Viproz/TNEV-Project/src/UltrasonicSensorCarriage.h

/* 
 * File:   UltrasonicSensorCarriage.h
 * Author: viproz
 *
 * Created on 17 mai 2015, 20:25
 */

#ifndef ULTRASONICSENSORCARRIAGE_H
#define	ULTRASONICSENSORCARRIAGE_H
#include "UltrasonicSensor.h"
#include "Servo.h"
#include <Arduino.h>

class UltrasonicSensorCarriage {
public:
    UltrasonicSensorCarriage();
    virtual ~UltrasonicSensorCarriage();
    void findNearest(int& angle, int& distance);
    int getDistance();
    void reset();
    void write(int angle) { servo->write(angle); }
private:
    Servo* servo;
    UltrasonicSensor* sensor;
    
};

#endif	/* ULTRASONICSENSORCARRIAGE_H */
