Viproz/TNEV-Project/src/Button.cpp

/* 
 * File:   Button.cpp
 * Author: viproz
 * 
 * Created on 31 mai 2015, 17:24
 */

#include "Button.h"

Button::Button(uint8_t pinButton) :
    pinButton(pinButton) {
    pinMode(pinButton, INPUT);
    pressed = false;
}

Button::~Button() {
}

/**
 * Reads the value of the pin and compares it with his previous state
 * 
 * This function will at the same time tick the pin and analyse the data, 
 * it has to be called frequently.
 * 
 * @return true if the button has been pushed
 */
bool Button::pushed() {
    int state = digitalRead(pinButton);
    
    //Only return true when the button has been released
    if(state == LOW && pressed) {
        pressed = false;
        return true;
    }
    
    pressed = state == HIGH;
    
    return false;
}
